idoroseman/dj-midi-controller/doc/IMG_1013.jpg

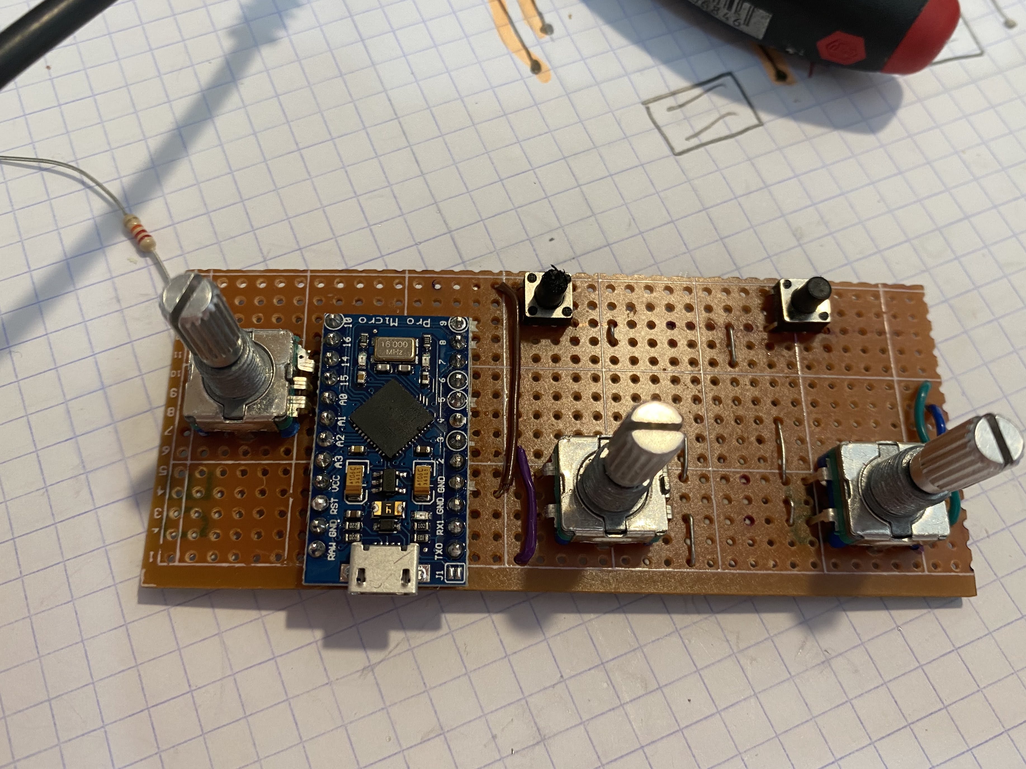
doc/IMG_1013.jpg
